markdlehane/RobinUSBC-PDM/Media/RDSPB5331A-Circuit.jpg

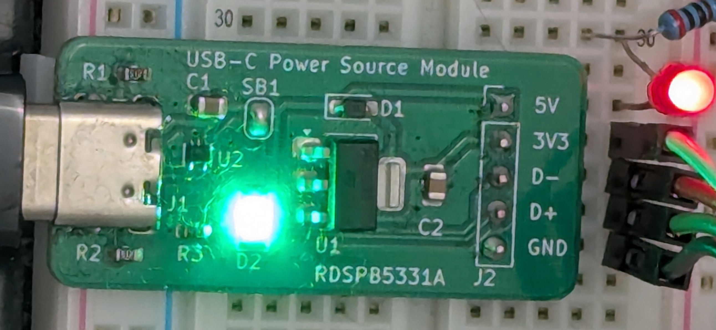
Media/RDSPB5331A-Circuit.jpg
