markdlehane/RobinUSBC-PDM/Media/RDSPB5331A.jpg

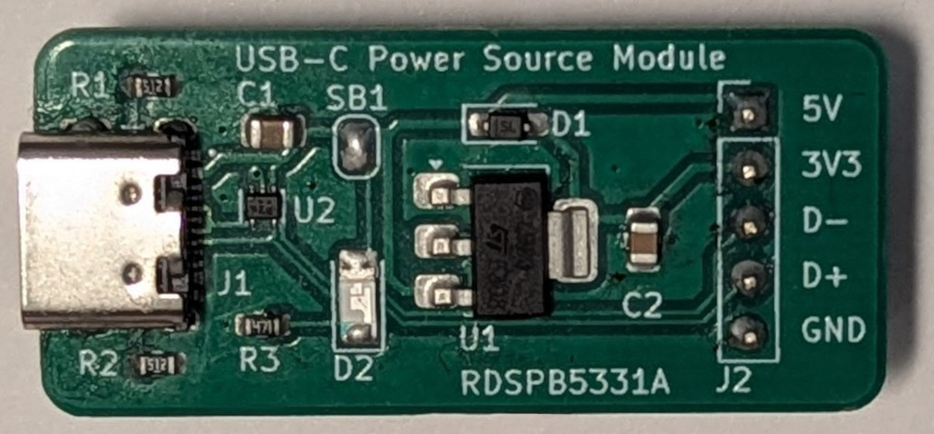
Media/RDSPB5331A.jpg
