markdlehane/RobinUSBC-PDM/Media/RobinUSBC-back-PSM.png

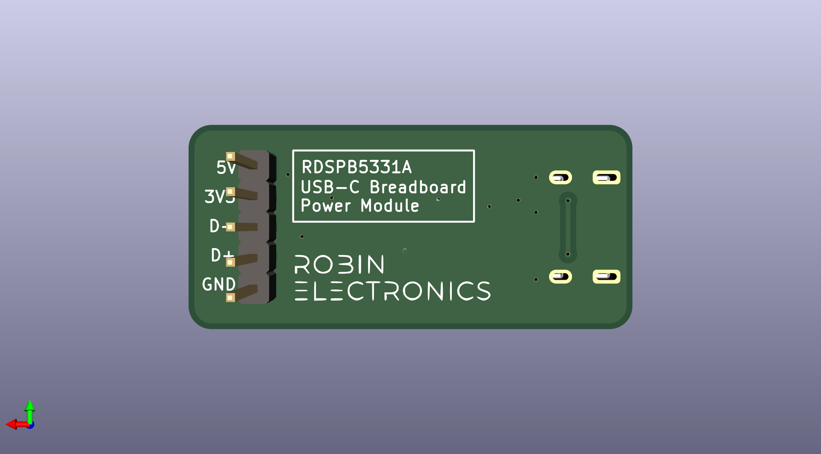
Media/RobinUSBC-back-PSM.png
