markdlehane/RobinUSBC-PDM/Media/RobinUSBC-Front-PSM.png

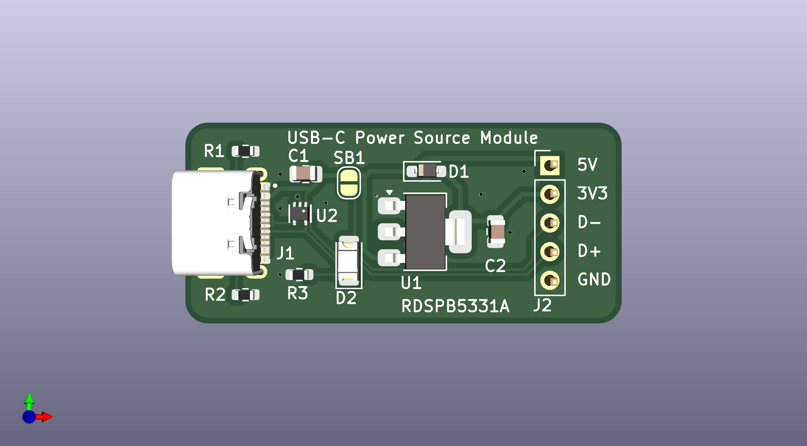
Media/RobinUSBC-Front-PSM.png
