markdlehane/RobinUSBC-PDM/NonGit/Media/PXL_20241114_135255856.jpg

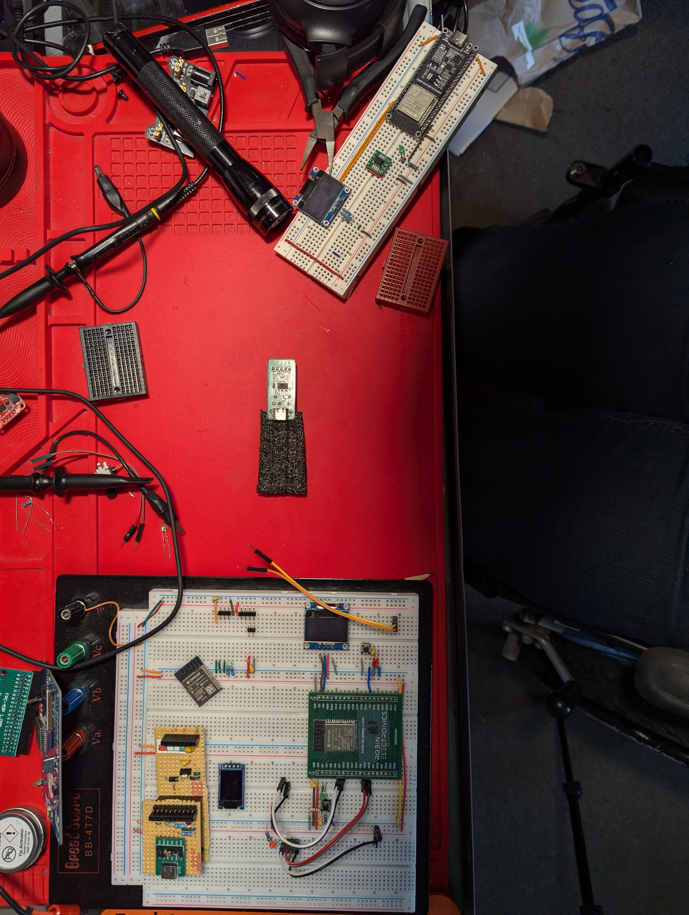
NonGit/Media/PXL_20241114_135255856.jpg
