markdlehane/RobinUSBC-PDM/NonGit/Media/PXL_20241114_135540129.jpg

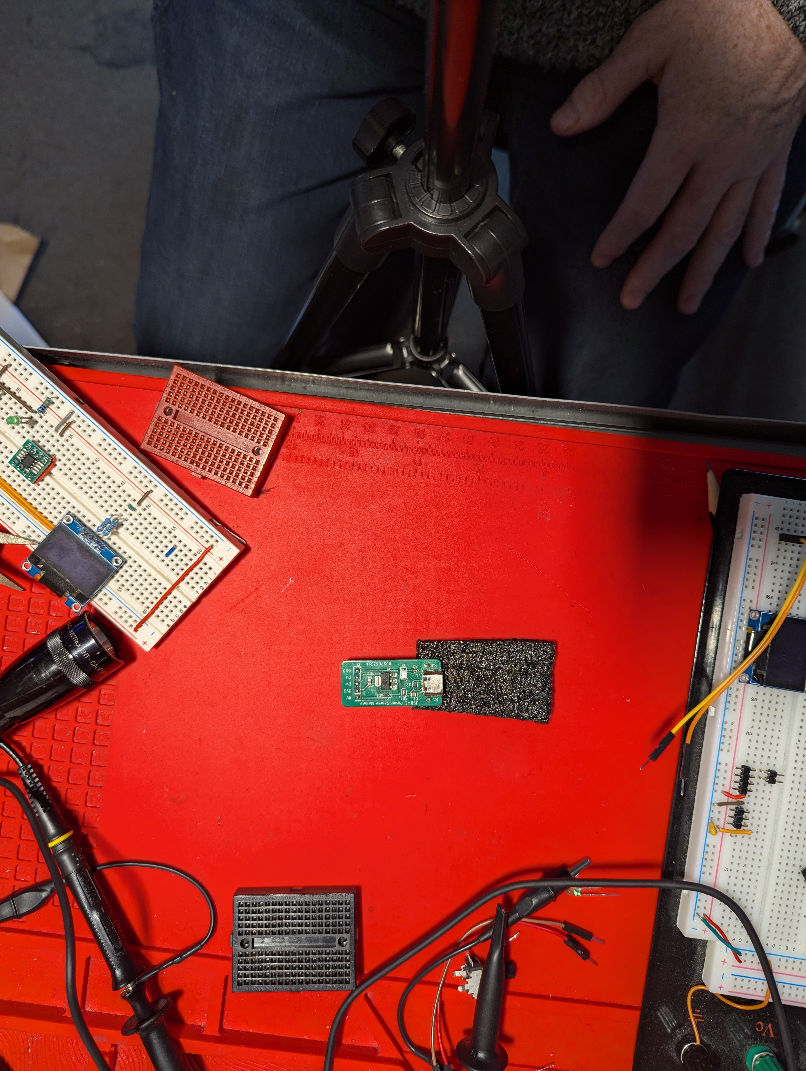
NonGit/Media/PXL_20241114_135540129.jpg
