markdlehane/RobinUSBC-PDM/NonGit/Media/PXL_20241114_135550647.jpg

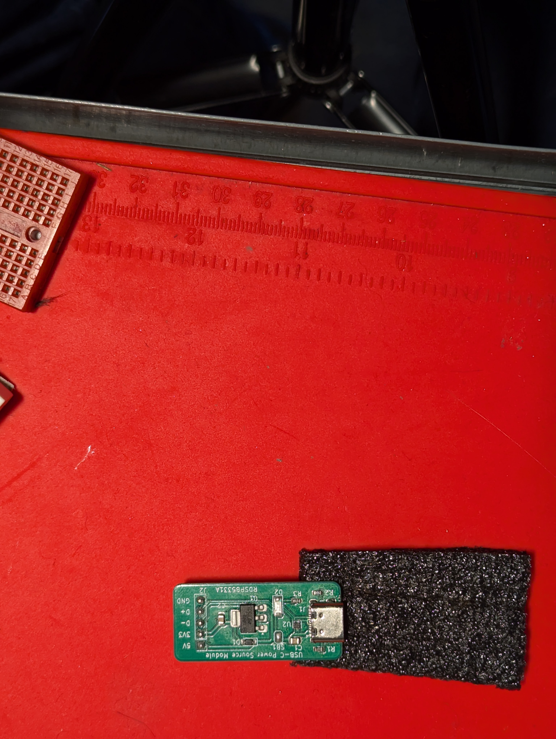
NonGit/Media/PXL_20241114_135550647.jpg
