markdlehane/RobinUSBC-PDM/NonGit/Media/PXL_20241114_135628191.PORTRAIT.jpg

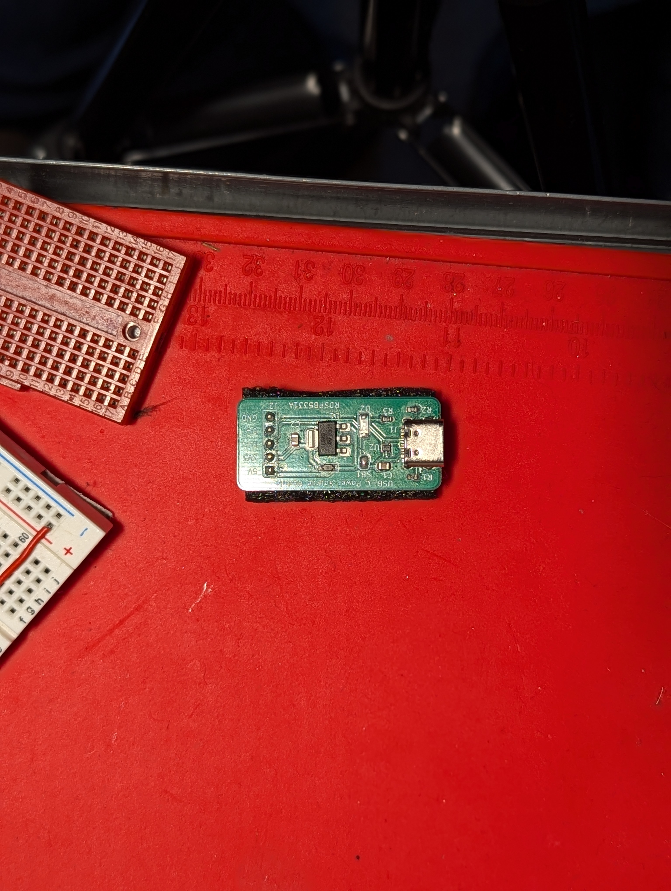
NonGit/Media/PXL_20241114_135628191.PORTRAIT.jpg
