markdlehane/RobinUSBC-PDM/NonGit/Media/PXL_20241114_135838315.PORTRAIT.jpg

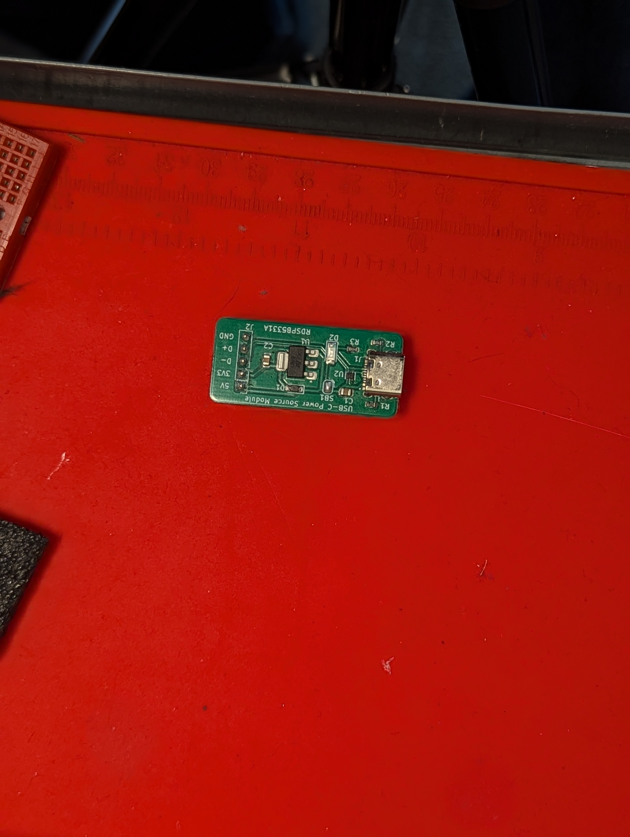
NonGit/Media/PXL_20241114_135838315.PORTRAIT.jpg
