markdlehane/RobinUSBC-PDM/NonGit/Media/PXL_20241114_135842290.PORTRAIT.jpg

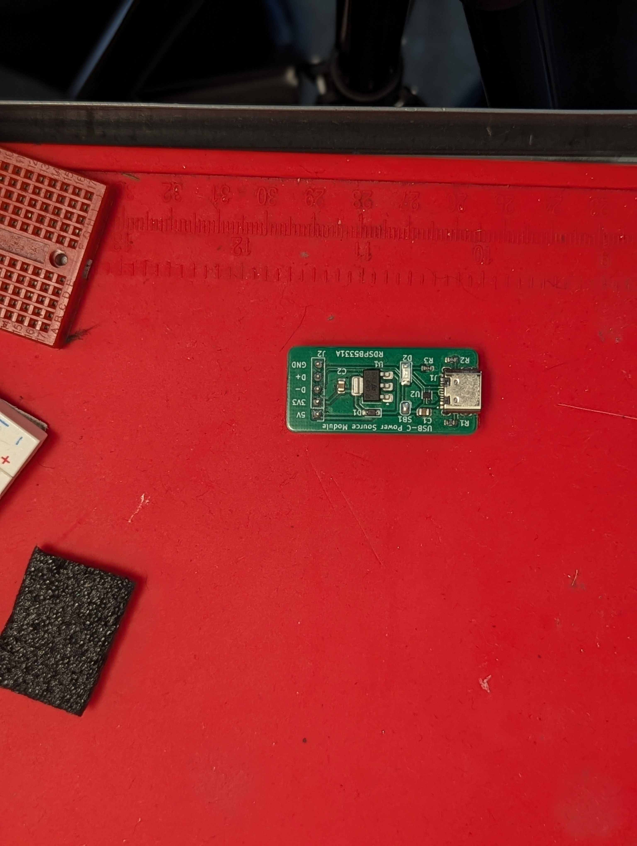
NonGit/Media/PXL_20241114_135842290.PORTRAIT.jpg
