markdlehane/RobinUSBC-PDM/NonGit/Media/PXL_20241114_135845703.PORTRAIT~2.jpg

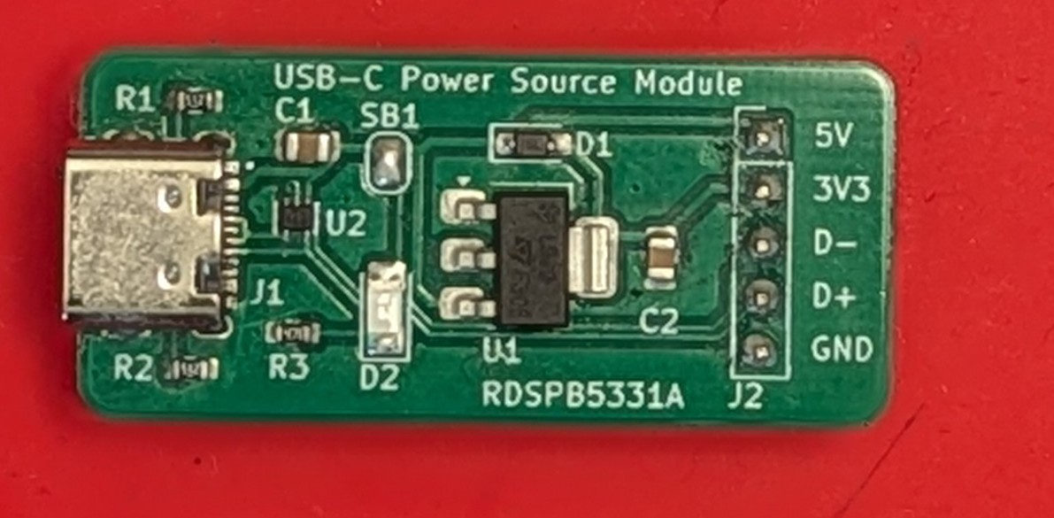
NonGit/Media/PXL_20241114_135845703.PORTRAIT~2.jpg
