markdlehane/RobinUSBC-PDM/NonGit/Media/PXL_20241114_141910397.RAW-01.COVER.jpg

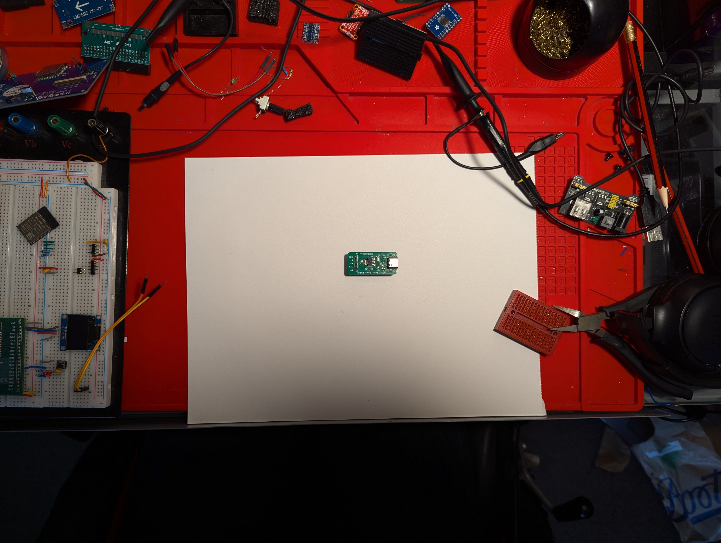
NonGit/Media/PXL_20241114_141910397.RAW-01.COVER.jpg
