markdlehane/RobinUSBC-PDM/NonGit/Media/PXL_20241114_141911273.RAW-01.COVER.jpg

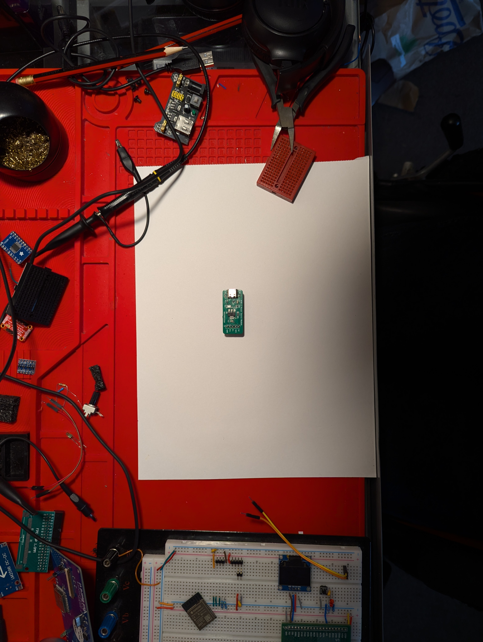
NonGit/Media/PXL_20241114_141911273.RAW-01.COVER.jpg
