markdlehane/RobinUSBC-PDM/NonGit/Media/PXL_20241114_142011990.PORTRAIT.ORIGINAL.jpg

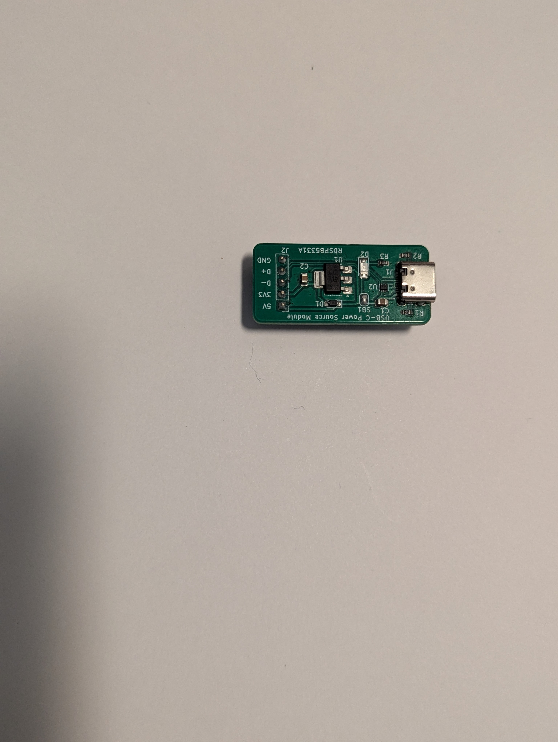
NonGit/Media/PXL_20241114_142011990.PORTRAIT.ORIGINAL.jpg
