markdlehane/RobinUSBC-PDM/NonGit/Media/PXL_20241114_142013790.PORTRAIT.ORIGINAL.jpg

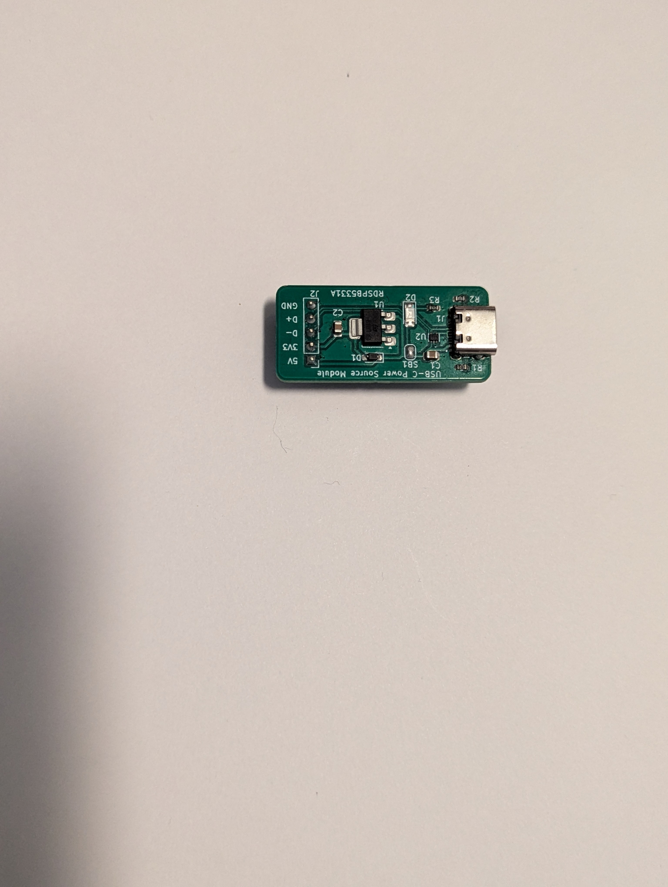
NonGit/Media/PXL_20241114_142013790.PORTRAIT.ORIGINAL.jpg
