markdlehane/RobinUSBC-PDM/NonGit/Media/PXL_20241114_142018524.PORTRAIT.jpg

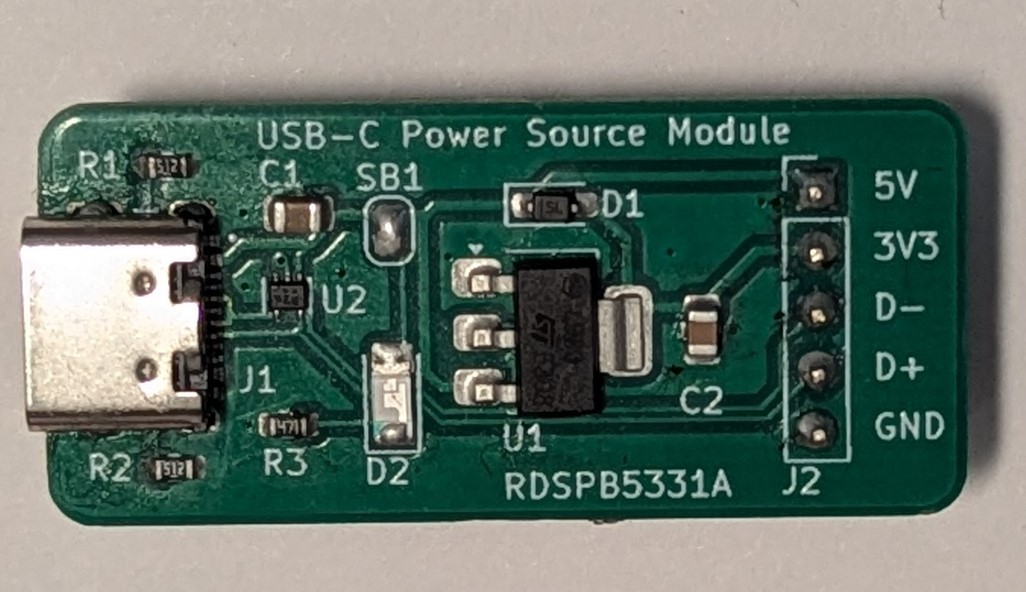
NonGit/Media/PXL_20241114_142018524.PORTRAIT.jpg
