markdlehane/RobinUSBC-PDM/NonGit/Media/PXL_20241124_144554496.RAW-01.COVER.jpg

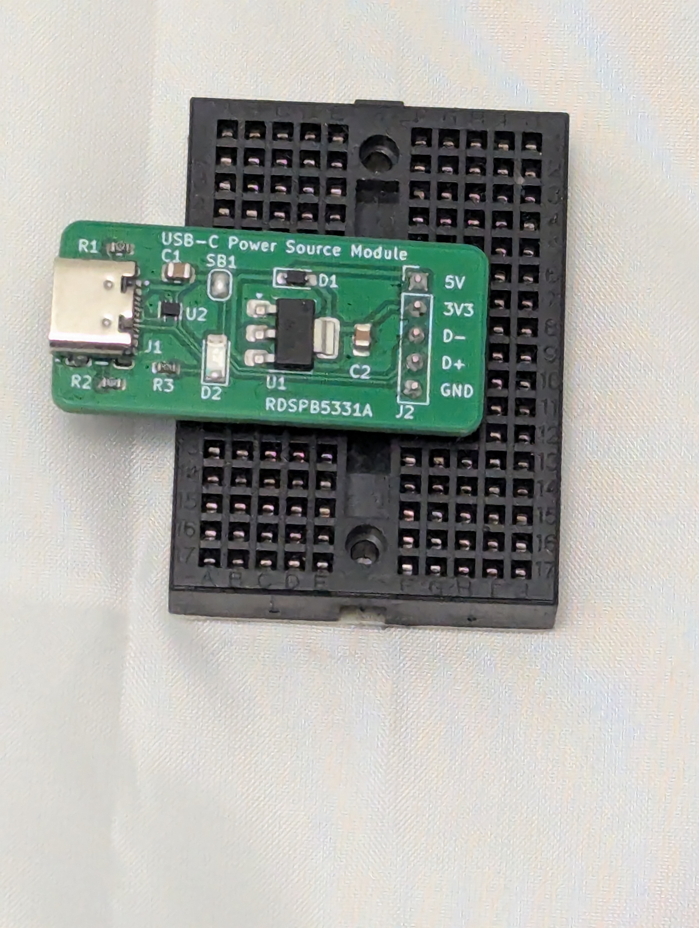
NonGit/Media/PXL_20241124_144554496.RAW-01.COVER.jpg
