markdlehane/RobinUSBC-PDM/NonGit/Media/PXL_20241124_144603792.RAW-01.COVER.jpg

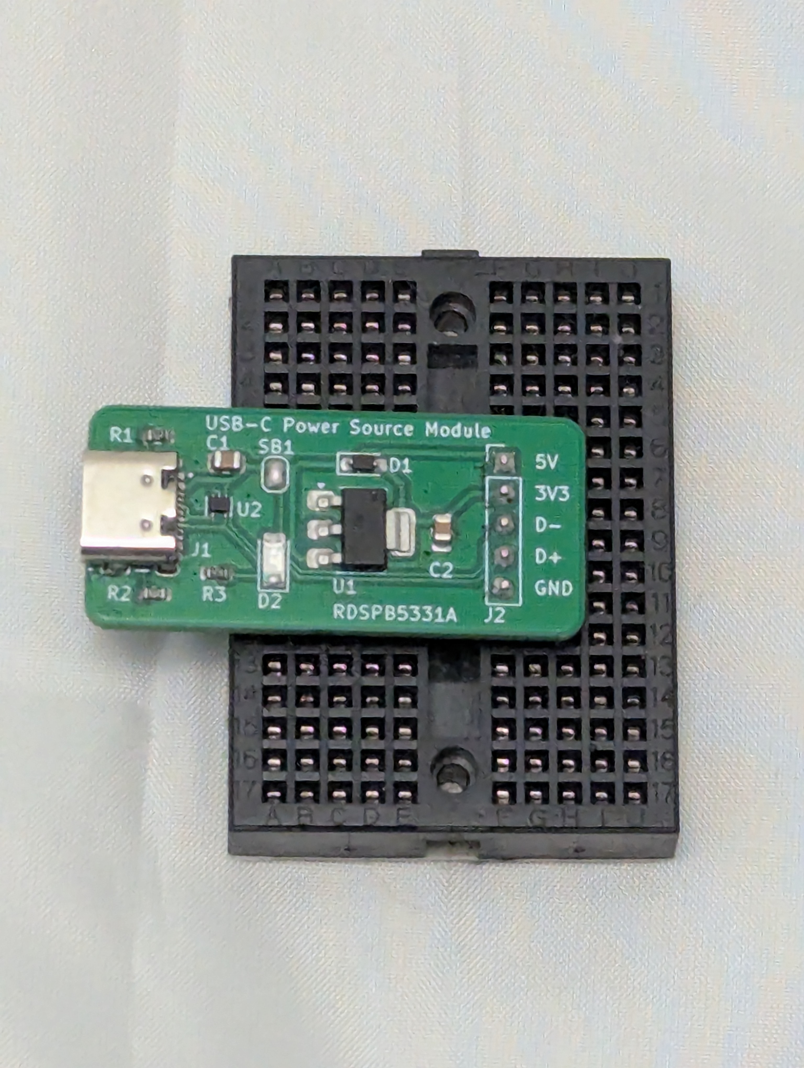
NonGit/Media/PXL_20241124_144603792.RAW-01.COVER.jpg
