markdlehane/RobinUSBC-PDM/NonGit/Media/PXL_20241124_144744057.RAW-01.COVER.jpg

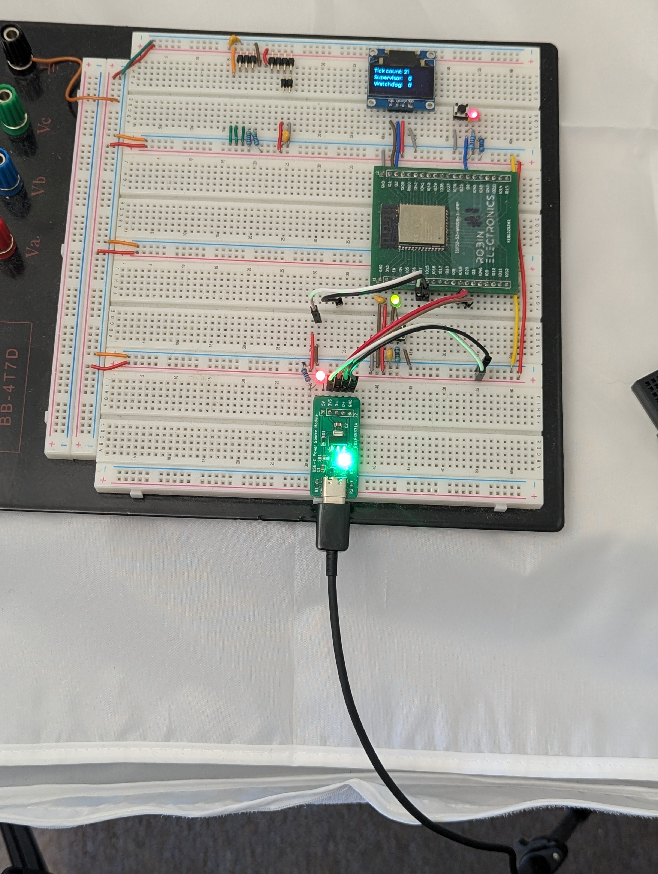
NonGit/Media/PXL_20241124_144744057.RAW-01.COVER.jpg
