markdlehane/RobinUSBC-PDM/NonGit/Media/PXL_20241124_144805324.RAW-01.COVER.jpg

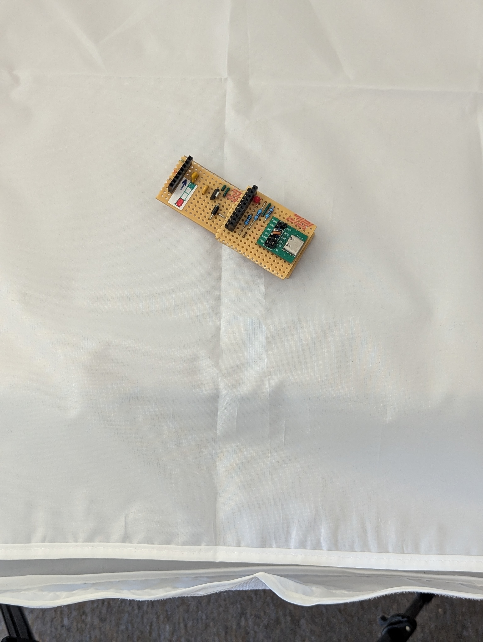
NonGit/Media/PXL_20241124_144805324.RAW-01.COVER.jpg
