markdlehane/RobinUSBC-PDM/NonGit/Media/PXL_20241124_145244134.RAW-01.COVER.jpg

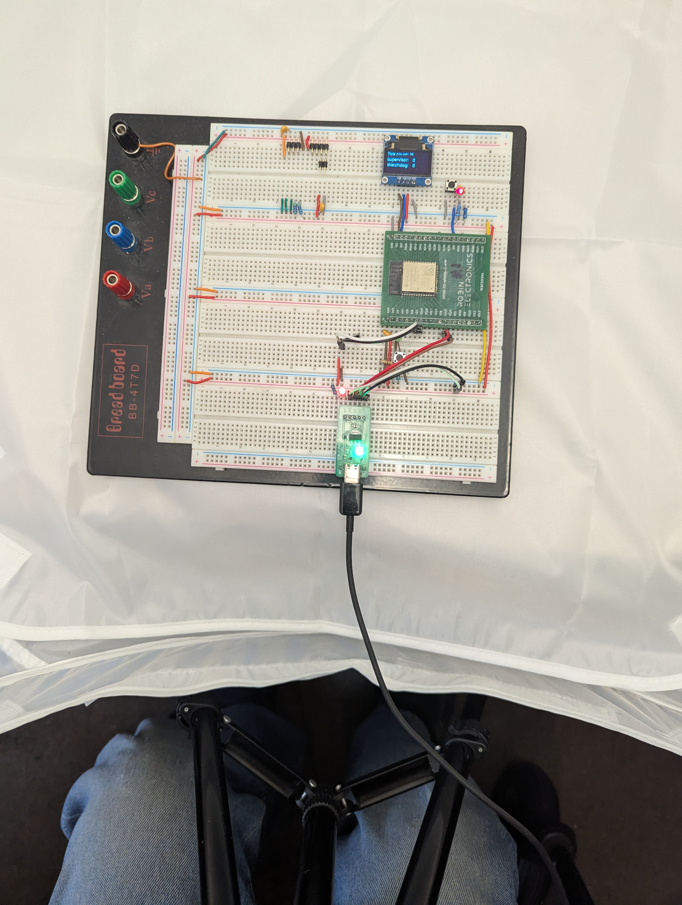
NonGit/Media/PXL_20241124_145244134.RAW-01.COVER.jpg
