markdlehane/RobinUSBC-PDM/NonGit/Media/PXL_20241124_145702664.RAW-01.COVER.jpg

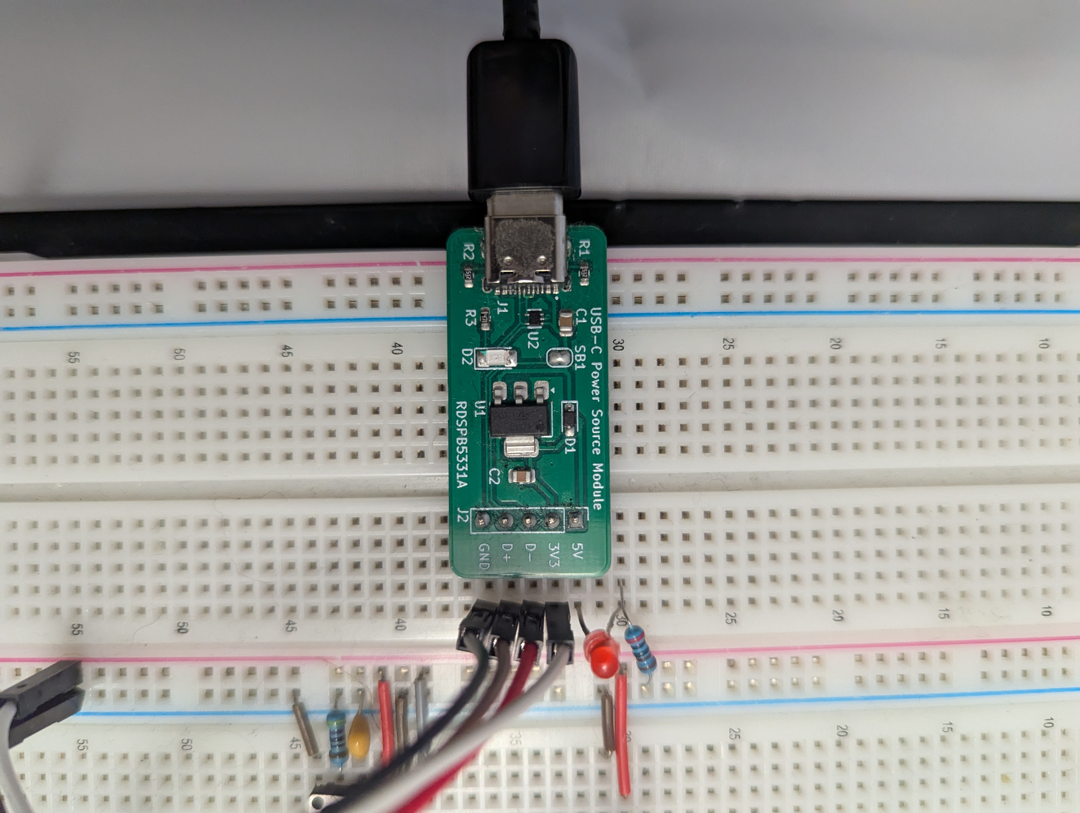
NonGit/Media/PXL_20241124_145702664.RAW-01.COVER.jpg
