markdlehane/RobinUSBC-PDM/NonGit/Media/PXL_20241124_145704431.RAW-01.COVER.jpg

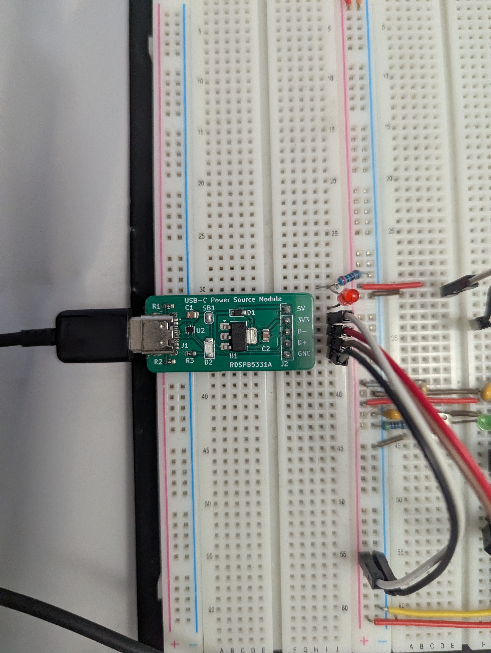
NonGit/Media/PXL_20241124_145704431.RAW-01.COVER.jpg
