markdlehane/RobinUSBC-PDM/NonGit/Media/RDSPB5331A-InCircuit.jpg

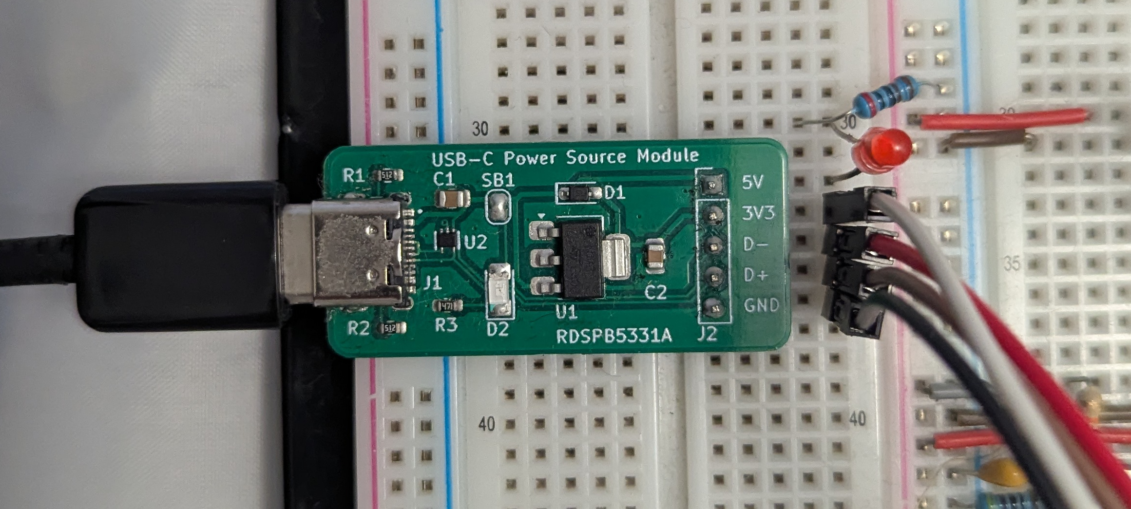
NonGit/Media/RDSPB5331A-InCircuit.jpg
